DrZedEau/CM5_NavBridge/images/rpi_flash/PXL_20260627_122455078.jpg

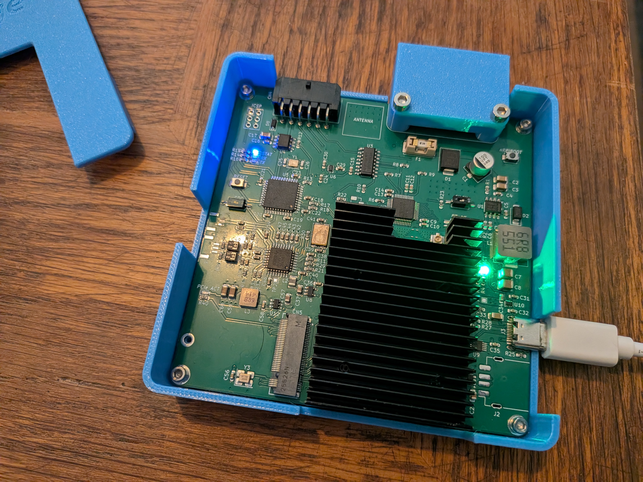
images/rpi_flash/PXL_20260627_122455078.jpg
