DrZedEau/CM5_NavBridge/images/rpi_flash/PXL_20260627_122511295.MP.jpg

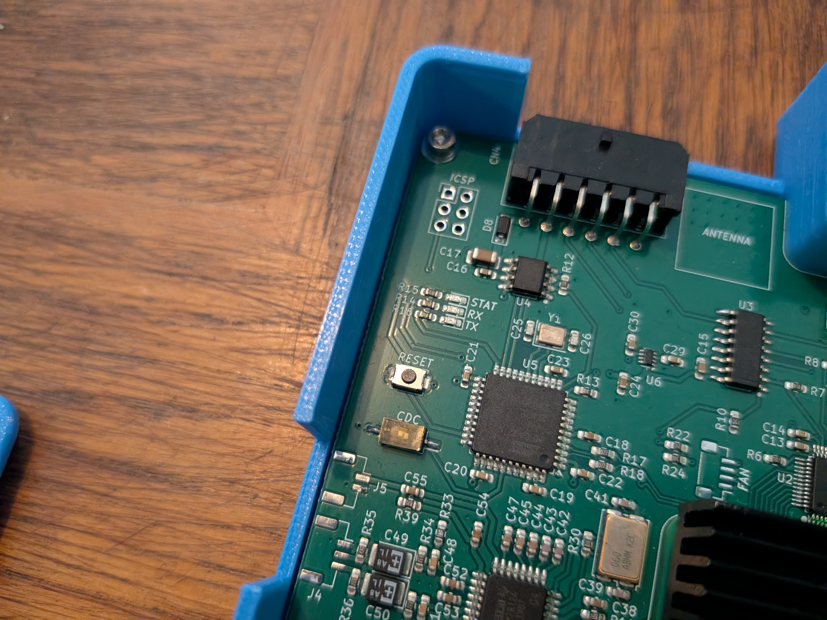
images/rpi_flash/PXL_20260627_122511295.MP.jpg
