DrZedEau/CM5_NavBridge/images/rpi_flash/PXL_20260627_122519090.jpg

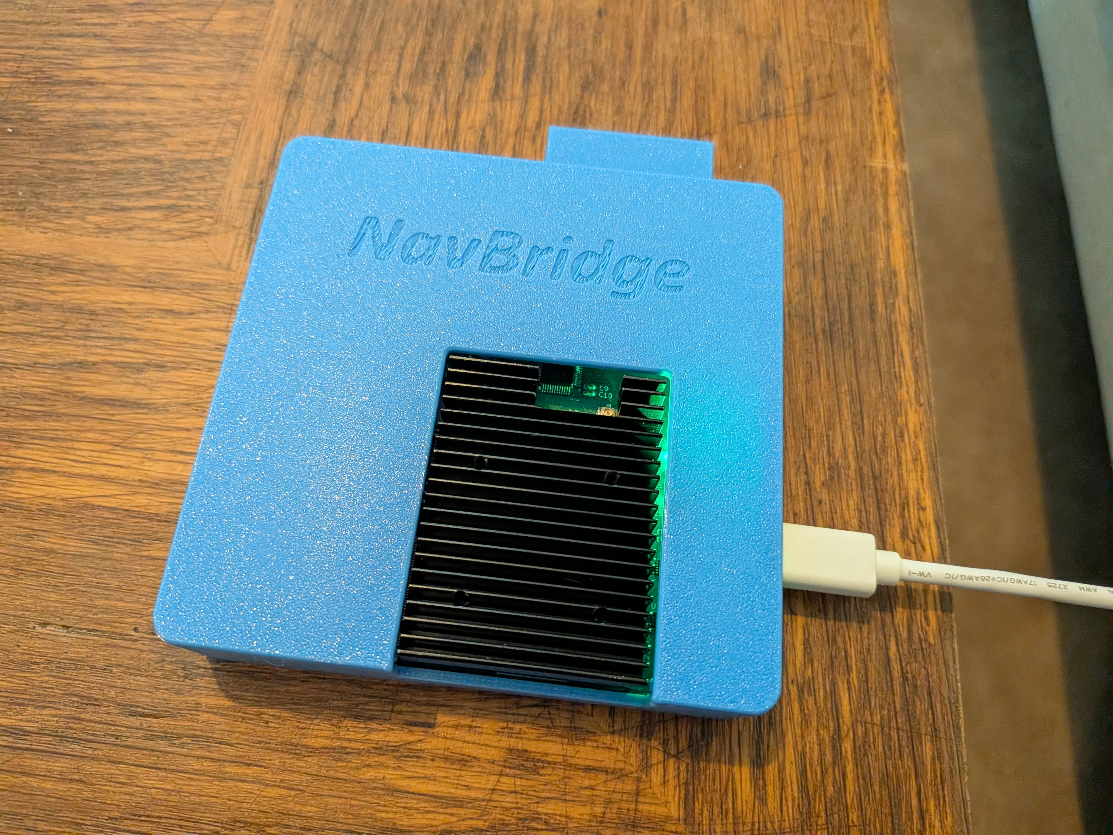
images/rpi_flash/PXL_20260627_122519090.jpg
