DrZedEau/CM5_NavBridge/images/Installation/PXL_20260427_113937315.jpg

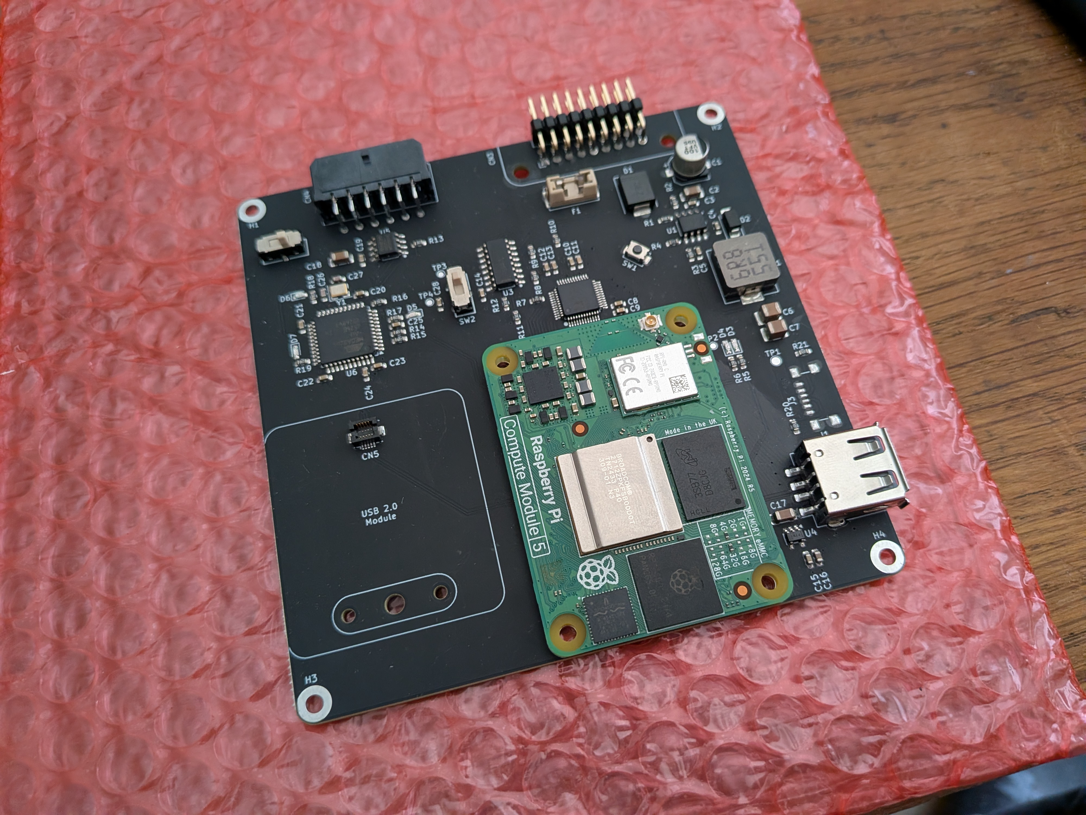
images/Installation/PXL_20260427_113937315.jpg
